anton2785-bit/anton2785-bit-Anton_s-Keyboard/Images/Keyboard case.png

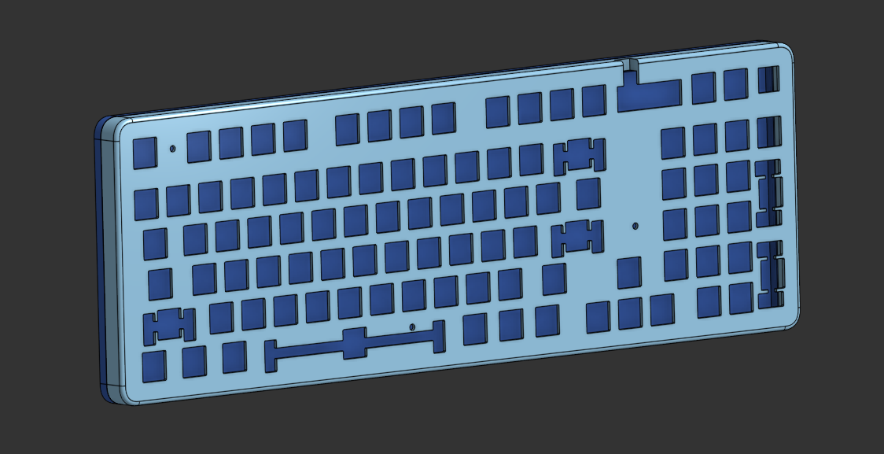
Images/Keyboard case.png
