anton2785-bit/anton2785-bit-Anton_s-Keyboard/Images/Top layer PCB.png

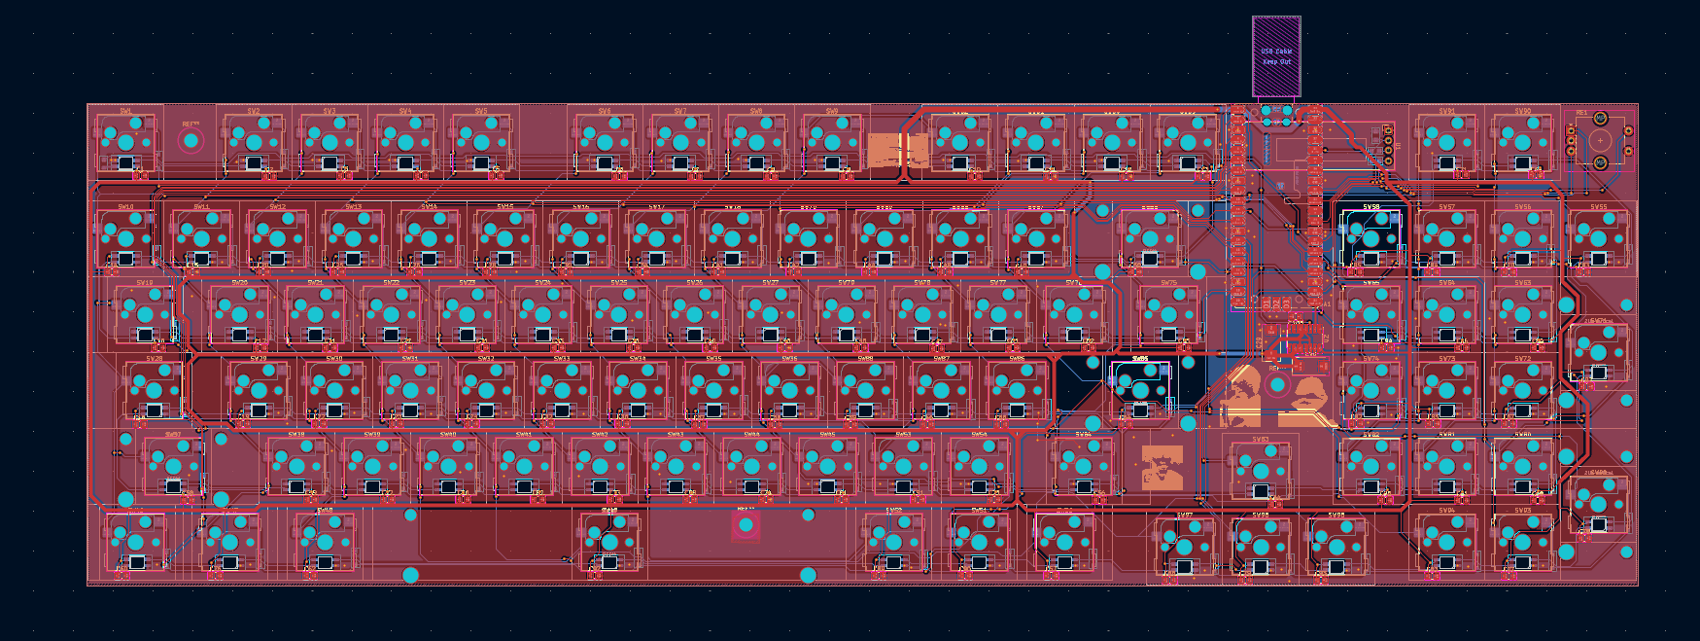
Images/Top layer PCB.png
