anton2785-bit/anton2785-bit-Anton_s-Keyboard/PCB/keyboard.kicad_sch

## KiCad design PCB/keyboard.kicad_sch (2026-03-09)

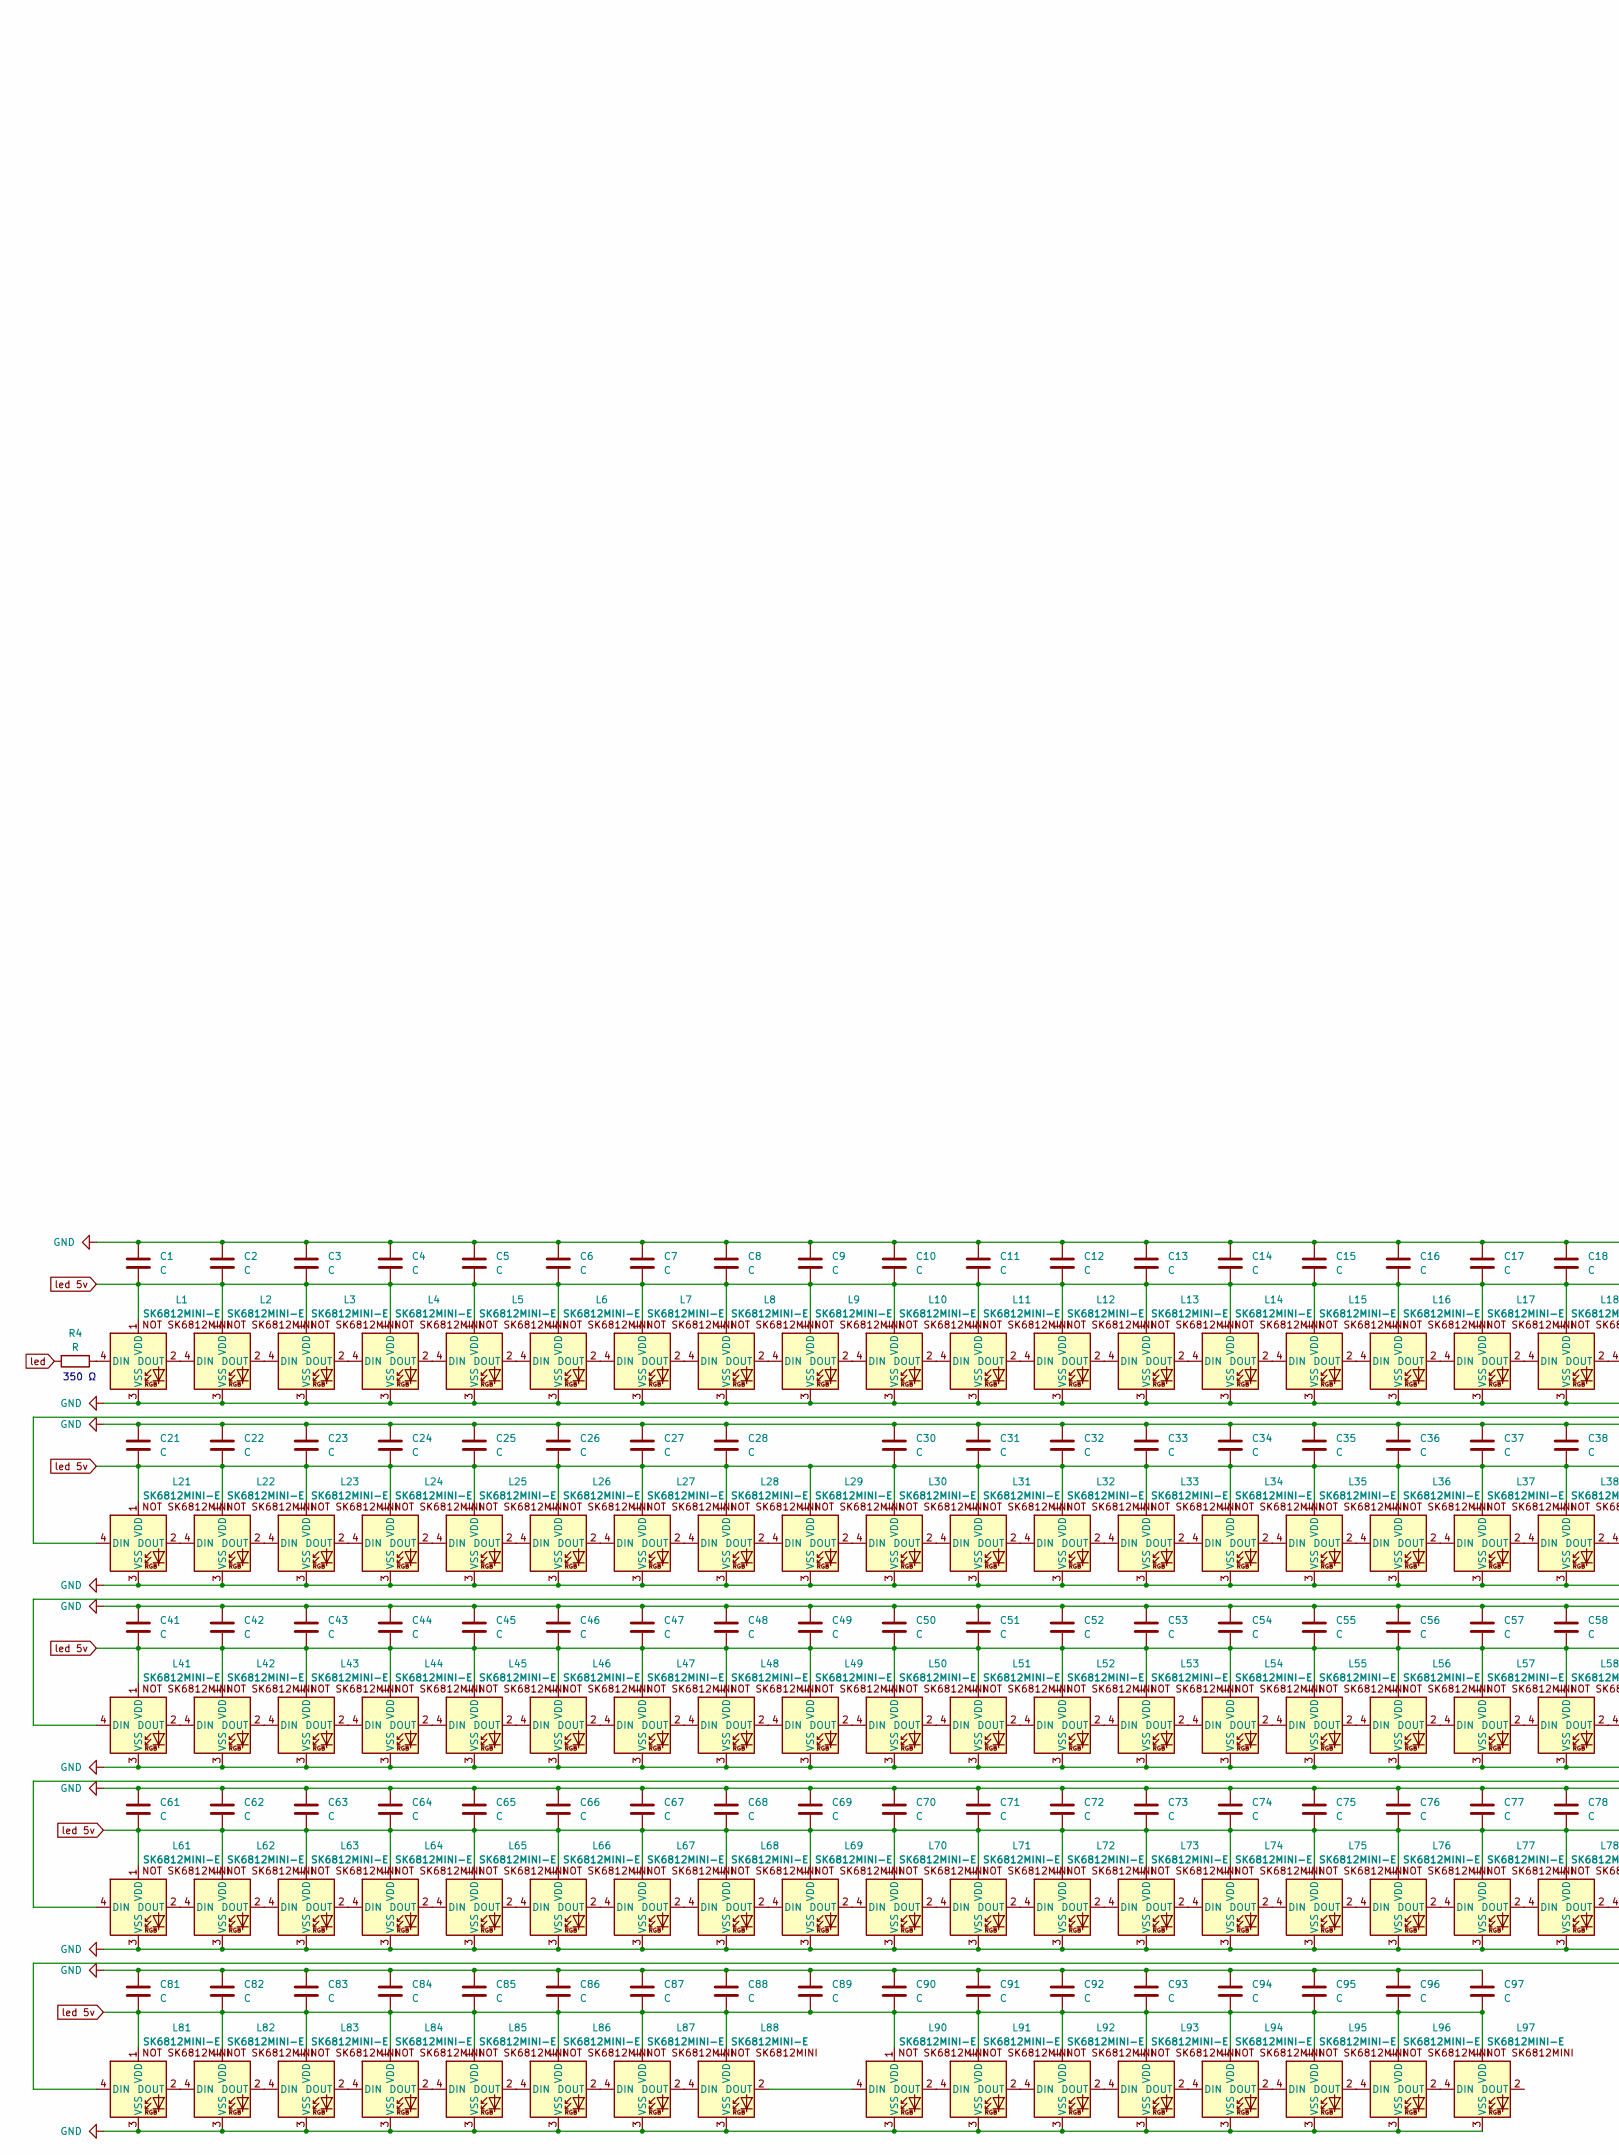
[picture p10: schematic keyboard.kicad_sch, part in row 1, column 1]

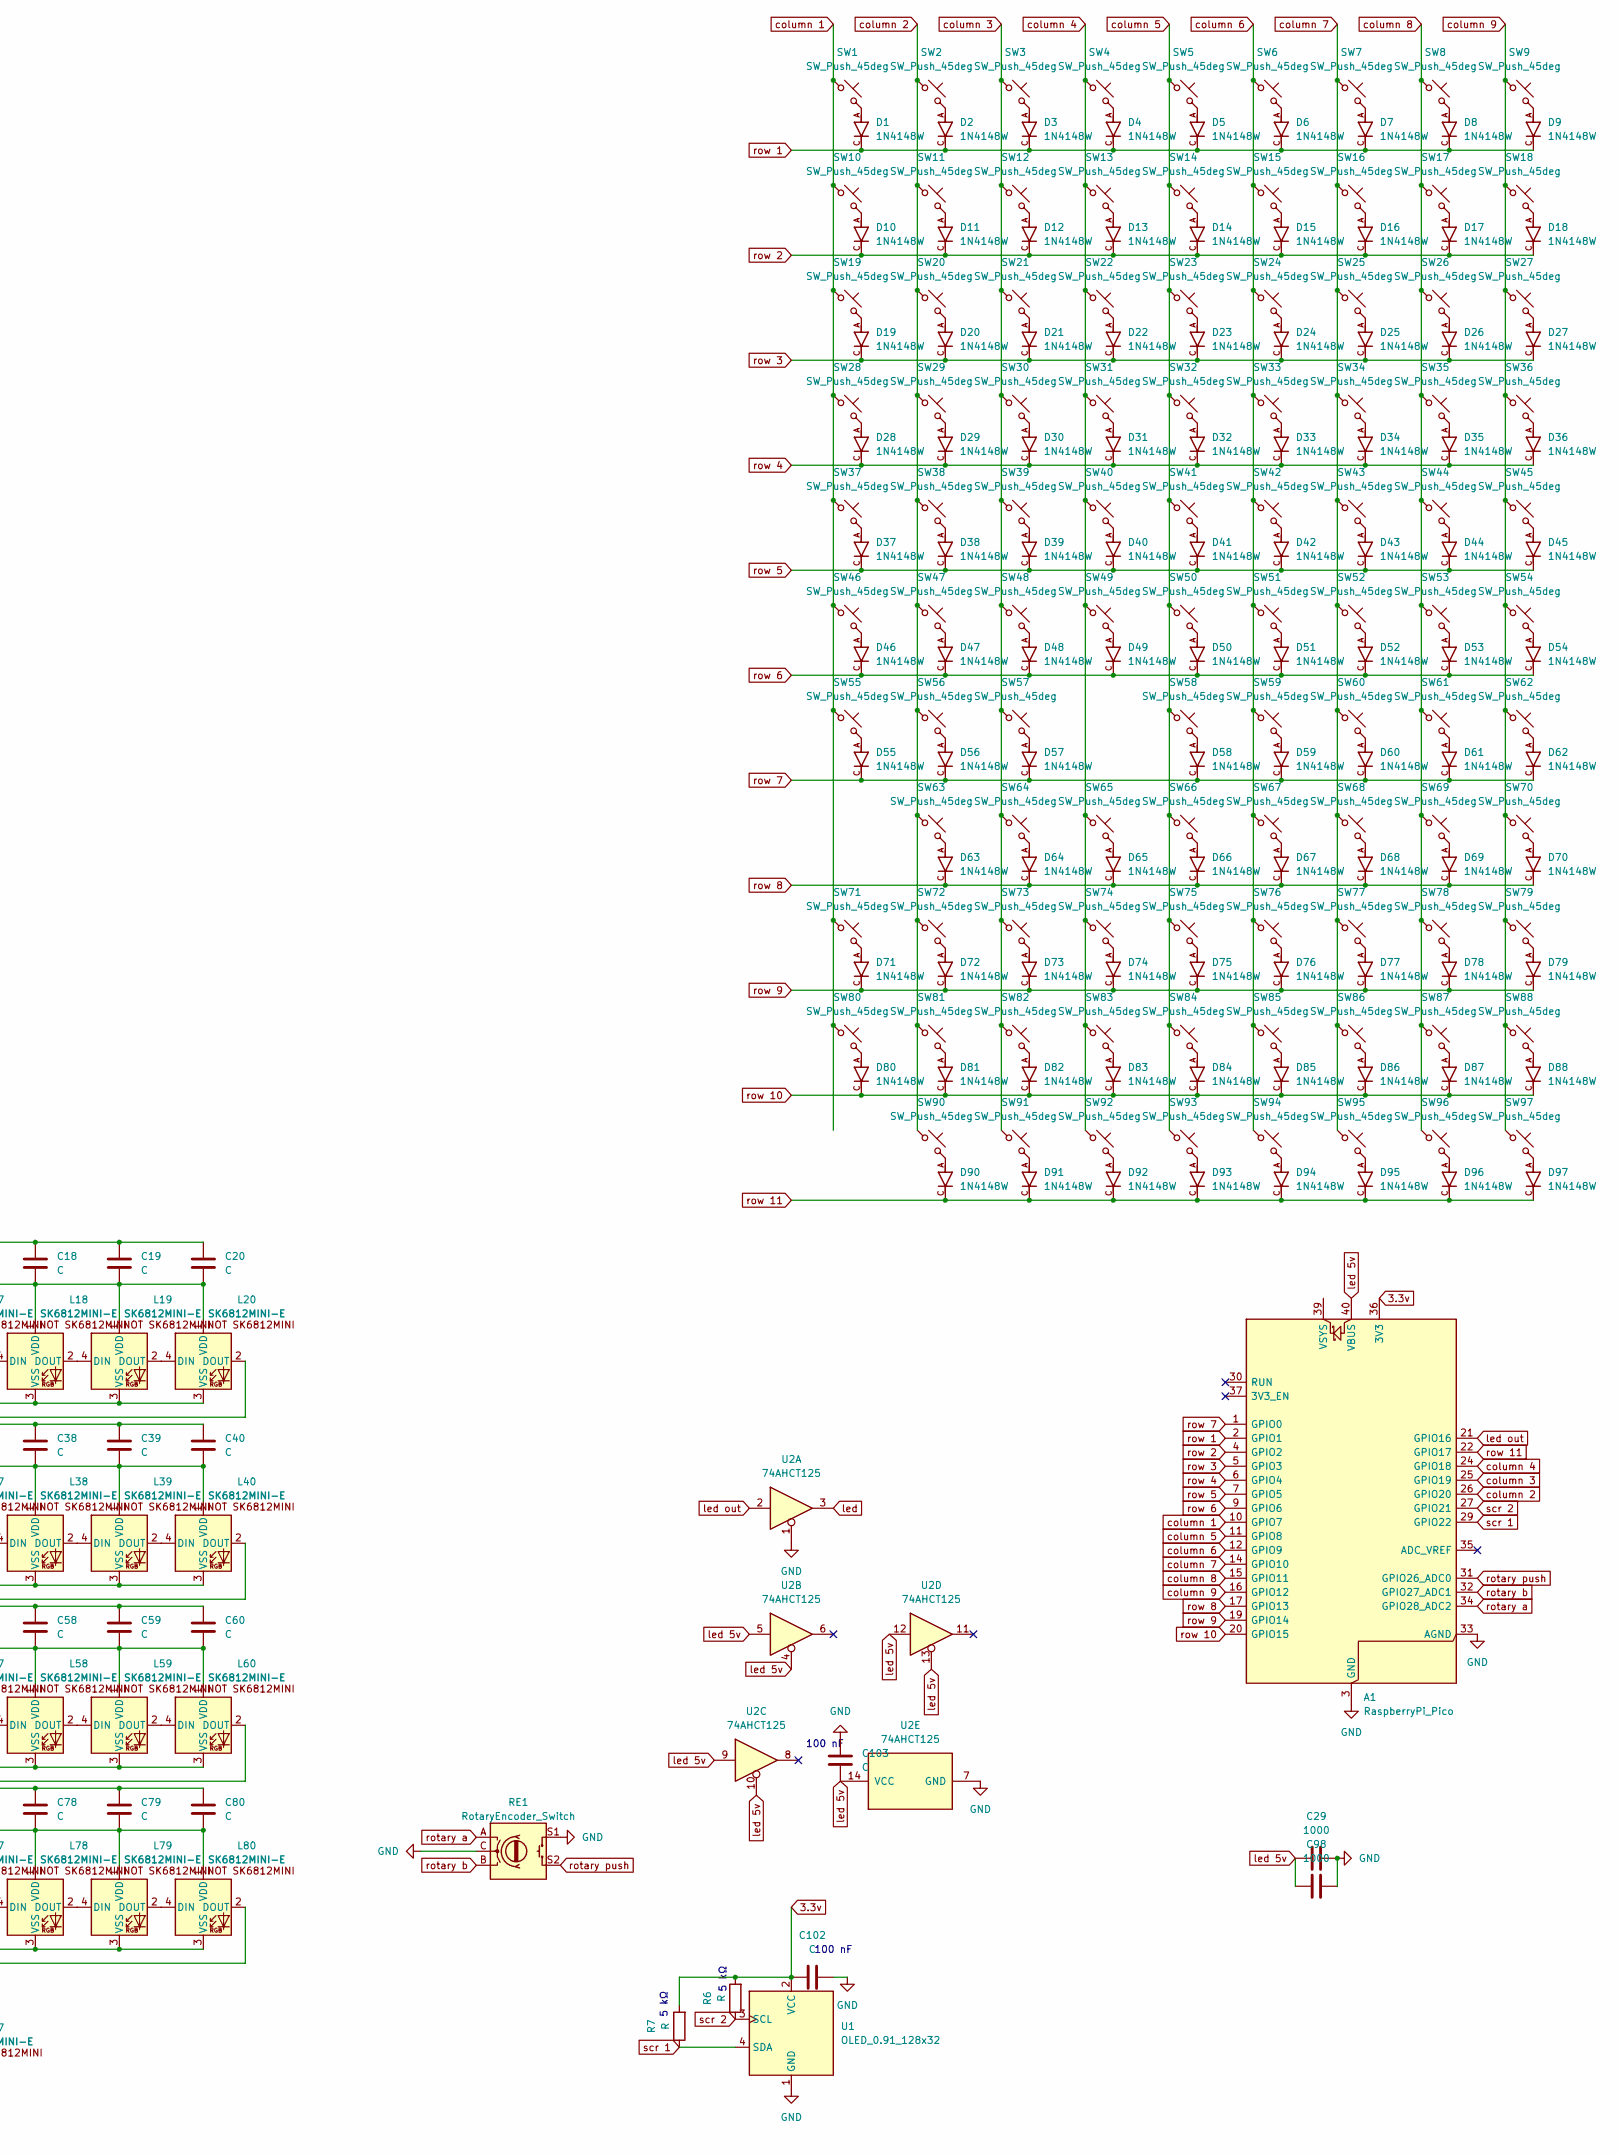
[picture p11: schematic keyboard.kicad_sch, part in row 1, column 2]

Parts:
A1: RaspberryPi_Pico; RaspberryPi_Pico_SMD_HandSolder
C1, C2, C3, C4, C5, C6, C7, C8, C9, C10, C11, C12, C13, C14, C15, C16, C17, C18, C19, C20, C21, C22, C23, C24, C25, C26, C27, C28, C30, C31, C32, C33, C34, C35, C36, C37, C38, C39, C40, C41, C42, C43, C44, C45, C46, C47, C48, C49, C50, C51, C52, C53, C54, C55, C56, C57, C58, C59, C60, C61, C62, C63, C64, C65, C66, C67, C68, C69, C70, C71, C72, C73, C74, C75, C76, C77, C78, C79, C80, C81, C82, C83, C84, C85, C86, C87, C88, C89, C90, C91, C92, C93, C94, C95, C96, C97, C102, C103: C; C_0805_2012Metric_Pad1.18x1.45mm_HandSolder
C29, C98: 1000; CP_EIA-7343-31_Kemet-D_HandSolder
D1, D2, D3, D4, D5, D6, D7, D8, D9, D10, D11, D12, D13, D14, D15, D16, D17, D18, D19, D20, D21, D22, D23, D24, D25, D26, D27, D28, D29, D30, D31, D32, D33, D34, D35, D36, D37, D38, D39, D40, D41, D42, D43, D44, D45, D46, D47, D48, D49, D50, D51, D52, D53, D54, D55, D56, D57, D58, D59, D60, D61, D62, D63, D64, D65, D66, D67, D68, D69, D70, D71, D72, D73, D74, D75, D76, D77, D78, D79, D80, D81, D82, D83, D84, D85, D86, D87, D88, D90, D91, D92, D93, D94, D95, D96, D97: 1N4148W; SODFL3816X120N; PARTREV 2021-07-12
L1, L2, L3, L4, L5, L6, L7, L8, L9, L10, L11, L12, L13, L28, L29, L30, L31, L32, L33, L34, L35, L36, L37, L38, L39, L40, L41, L55, L56, L57, L58, L59, L60, L61, L62, L63, L64, L65, L66, L67, L68, L69, L70, L74, L75, L76, L80, L81: SK6812MINI-E; MX_sk6812_mini_e_v1
L14, L15, L16, L17, L18, L19, L20, L21, L22, L23, L24, L25, L26, L27, L42, L43, L44, L45, L46, L47, L48, L49, L50, L51, L52, L53, L54, L71, L72, L73, L77, L78, L79, L82, L83, L84, L85, L86, L87, L88, L90, L91, L92, L93, L94, L95, L96, L97: SK6812MINI-E; MX_sk6812_mini_e_v1_rotated
R4, R6, R7: R; R_0805_2012Metric_Pad1.20x1.40mm_HandSolder
RE1: RotaryEncoder_Switch; RotaryEncoder_Alps_EC11E-Switch_Vertical_H20mm_CircularMoun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
SW1, SW2, SW3, SW4, SW5, SW6, SW7, SW8, SW9, SW10, SW11, SW12, SW13, SW14, SW15, SW16, SW17, SW18, SW20, SW21, SW22, SW23, SW24, SW25, SW26, SW27, SW29, SW30, SW31, SW32, SW33, SW34, SW35, SW36, SW38, SW39, SW40, SW41, SW42, SW43, SW44, SW45, SW53, SW54, SW55, SW56, SW57, SW58, SW59, SW60, SW61, SW62, SW63, SW64, SW65, SW67, SW68, SW69, SW70, SW72, SW73, SW74, SW76, SW77, SW78, SW79, SW80, SW81, SW82, SW83, SW86, SW87, SW88, SW90, SW91, SW93, SW94, SW95, SW96, SW97: SW_Push_45deg; Hotswap_MX_1.00u
SW19, SW75: SW_Push_45deg; Hotswap_MX_1.50u
SW28, SW84: SW_Push_45deg; Hotswap_MX_1.75u
SW37, SW85: SW_Push_45deg; Hotswap_MX_2.25u
SW46, SW47, SW48, SW50, SW51, SW52: SW_Push_45deg; Hotswap_MX_1.25u
SW49: SW_Push_45deg; Hotswap_MX_6.25u
SW66: SW_Push_45deg; Hotswap_MX_2.00u
SW71, SW92: SW_Push_45deg; Hotswap_MX_2.00u_90deg
U1: OLED_0.91_128x32
U2: 74AHCT125; SOIC-14_3.9x8.7mm_P1.27mm

Connections:
3.3v: A1.36 (3V3), C102.2, R6.2, R7.2, U1.2 (VCC)
GND: A1.3 (GND), A1.8 (GND), A1.13 (GND), A1.18 (GND), A1.23 (GND), A1.28 (GND), A1.33 (AGND), A1.38 (GND), C1.2, C2.2, C3.2, C4.2, C5.2, C6.2, C7.2, C8.2, C9.2, C10.2, C11.2, C12.2, C13.2, C14.2, C15.2, C16.2, C17.2, C18.2, C19.2, C20.2, C21.2, C22.2, C23.2, C24.2, C25.2, C26.2, C27.2, C28.2, C29.2, C30.2, C31.2, C32.2, C33.2, C34.2, C35.2, C36.2, C37.2, C38.2, C39.2, C40.2, C41.2, C42.2, C43.2, C44.2, C45.2, C46.2, C47.2, C48.2, C49.2, C50.2, C51.2, C52.2, C53.2, C54.2, C55.2, C56.2, C57.2, C58.2, C59.2, C60.2, C61.2, C62.2, C63.2, C64.2, C65.2, C66.2, C67.2, C68.2, C69.2, C70.2, C71.2, C72.2, C73.2, C74.2, C75.2, C76.2, C77.2, C78.2, C79.2, C80.2, C81.2, C82.2, C83.2, C84.2, C85.2, C86.2, C87.2, C88.2, C89.2, C90.2, C91.2, C92.2, C93.2, C94.2, C95.2, C96.2, C97.2, C98.2, C102.1, C103.2, L1.3 (VSS), L2.3 (VSS), L3.3 (VSS), L4.3 (VSS), L5.3 (VSS), L6.3 (VSS), L7.3 (VSS), L8.3 (VSS), L9.3 (VSS), L10.3 (VSS), L11.3 (VSS), L12.3 (VSS), L13.3 (VSS), L14.3 (VSS), L15.3 (VSS), L16.3 (VSS), L17.3 (VSS), L18.3 (VSS), L19.3 (VSS), L20.3 (VSS), L21.3 (VSS), L22.3 (VSS), L23.3 (VSS), L24.3 (VSS), L25.3 (VSS), L26.3 (VSS), L27.3 (VSS), L28.3 (VSS), L29.3 (VSS), L30.3 (VSS), L31.3 (VSS), L32.3 (VSS), L33.3 (VSS), L34.3 (VSS), L35.3 (VSS), L36.3 (VSS), L37.3 (VSS), L38.3 (VSS), L39.3 (VSS), L40.3 (VSS), L41.3 (VSS), L42.3 (VSS), L43.3 (VSS), L44.3 (VSS), L45.3 (VSS), L46.3 (VSS), L47.3 (VSS), L48.3 (VSS), L49.3 (VSS), L50.3 (VSS), L51.3 (VSS), L52.3 (VSS), L53.3 (VSS), L54.3 (VSS), L55.3 (VSS), L56.3 (VSS), L57.3 (VSS), L58.3 (VSS), L59.3 (VSS), L60.3 (VSS), L61.3 (VSS), L62.3 (VSS), L63.3 (VSS), L64.3 (VSS), L65.3 (VSS), L66.3 (VSS), L67.3 (VSS), L68.3 (VSS), L69.3 (VSS), L70.3 (VSS), L71.3 (VSS), L72.3 (VSS), L73.3 (VSS), L74.3 (VSS), L75.3 (VSS), L76.3 (VSS), L77.3 (VSS), L78.3 (VSS), L79.3 (VSS), L80.3 (VSS), L81.3 (VSS), L82.3 (VSS), L83.3 (VSS), L84.3 (VSS), L85.3 (VSS), L86.3 (VSS), L87.3 (VSS), L88.3 (VSS), L90.3 (VSS), L91.3 (VSS), L92.3 (VSS), L93.3 (VSS), L94.3 (VSS), L95.3 (VSS), L96.3 (VSS), L97.3 (VSS), RE1.C, RE1.S1, U1.1 (GND), U2.1, U2.7 (GND)
unnamed: D1.A, SW1.2
unnamed: D2.A, SW2.2
unnamed: D3.A, SW3.2
unnamed: D4.A, SW4.2
unnamed: D5.A, SW5.2
unnamed: D6.A, SW6.2
unnamed: D7.A, SW7.2
unnamed: D8.A, SW8.2
unnamed: D9.A, SW9.2
unnamed: D10.A, SW10.2
unnamed: D11.A, SW11.2
unnamed: D12.A, SW12.2
unnamed: D13.A, SW13.2
unnamed: D14.A, SW14.2
unnamed: D15.A, SW15.2
unnamed: D16.A, SW16.2
unnamed: D17.A, SW17.2
unnamed: D18.A, SW18.2
unnamed: D19.A, SW19.2
unnamed: D20.A, SW20.2
unnamed: D21.A, SW21.2
unnamed: D22.A, SW22.2
unnamed: D23.A, SW23.2
unnamed: D24.A, SW24.2
unnamed: D25.A, SW25.2
unnamed: D26.A, SW26.2
unnamed: D27.A, SW27.2
unnamed: D28.A, SW28.2
unnamed: D29.A, SW29.2
unnamed: D30.A, SW30.2
unnamed: D31.A, SW31.2
unnamed: D32.A, SW32.2
unnamed: D33.A, SW33.2
unnamed: D34.A, SW34.2
unnamed: D35.A, SW35.2
unnamed: D36.A, SW36.2
unnamed: D37.A, SW37.2
unnamed: D38.A, SW38.2
unnamed: D39.A, SW39.2
unnamed: D40.A, SW40.2
unnamed: D41.A, SW41.2
unnamed: D42.A, SW42.2
unnamed: D43.A, SW43.2
unnamed: D44.A, SW44.2
unnamed: D45.A, SW45.2
unnamed: D46.A, SW46.2
unnamed: D47.A, SW47.2
unnamed: D48.A, SW48.2
unnamed: D49.A, SW49.2
unnamed: D50.A, SW50.2
unnamed: D51.A, SW51.2
unnamed: D52.A, SW52.2
unnamed: D53.A, SW53.2
unnamed: D54.A, SW54.2
unnamed: D55.A, SW55.2
unnamed: D56.A, SW56.2
unnamed: D57.A, SW57.2
unnamed: D58.A, SW58.2
unnamed: D59.A, SW59.2
unnamed: D60.A, SW60.2
unnamed: D61.A, SW61.2
unnamed: D62.A, SW62.2
unnamed: D63.A, SW63.2
unnamed: D64.A, SW64.2
unnamed: D65.A, SW65.2
unnamed: D66.A, SW66.2
unnamed: D67.A, SW67.2
unnamed: D68.A, SW68.2
unnamed: D69.A, SW69.2
unnamed: D70.A, SW70.2
unnamed: D71.A, SW71.2
unnamed: D72.A, SW72.2
unnamed: D73.A, SW73.2
unnamed: D74.A, SW74.2
unnamed: D75.A, SW75.2
unnamed: D76.A, SW76.2
unnamed: D77.A, SW77.2
unnamed: D78.A, SW78.2
unnamed: D79.A, SW79.2
unnamed: D80.A, SW80.2
unnamed: D81.A, SW81.2
unnamed: D82.A, SW82.2
unnamed: D83.A, SW83.2
unnamed: D84.A, SW84.2
unnamed: D85.A, SW85.2
unnamed: D86.A, SW86.2
unnamed: D87.A, SW87.2
unnamed: D88.A, SW88.2
unnamed: D90.A, SW90.2
unnamed: D91.A, SW91.2
unnamed: D92.A, SW92.2
unnamed: D93.A, SW93.2
unnamed: D94.A, SW94.2
unnamed: D95.A, SW95.2
unnamed: D96.A, SW96.2
unnamed: D97.A, SW97.2
unnamed: L1.2 (DOUT), L2.4 (DIN)
unnamed: L1.4 (DIN), R4.1
unnamed: L2.2 (DOUT), L3.4 (DIN)
unnamed: L3.2 (DOUT), L4.4 (DIN)
unnamed: L4.2 (DOUT), L5.4 (DIN)
unnamed: L5.2 (DOUT), L6.4 (DIN)
unnamed: L6.2 (DOUT), L7.4 (DIN)
unnamed: L7.2 (DOUT), L8.4 (DIN)
unnamed: L8.2 (DOUT), L9.4 (DIN)
unnamed: L10.2 (DOUT), L11.4 (DIN)
unnamed: L9.2 (DOUT), L10.4 (DIN)
unnamed: L11.2 (DOUT), L12.4 (DIN)
unnamed: L12.2 (DOUT), L13.4 (DIN)
unnamed: L13.2 (DOUT), L14.4 (DIN)
unnamed: L14.2 (DOUT), L15.4 (DIN)
unnamed: L15.2 (DOUT), L16.4 (DIN)
unnamed: L16.2 (DOUT), L17.4 (DIN)
unnamed: L17.2 (DOUT), L18.4 (DIN)
unnamed: L18.2 (DOUT), L19.4 (DIN)
unnamed: L19.2 (DOUT), L20.4 (DIN)
unnamed: L20.2 (DOUT), L21.4 (DIN)
unnamed: L21.2 (DOUT), L22.4 (DIN)
unnamed: L22.2 (DOUT), L23.4 (DIN)
unnamed: L23.2 (DOUT), L24.4 (DIN)
unnamed: L24.2 (DOUT), L25.4 (DIN)
unnamed: L25.2 (DOUT), L26.4 (DIN)
unnamed: L26.2 (DOUT), L27.4 (DIN)
unnamed: L27.2 (DOUT), L28.4 (DIN)
unnamed: L28.2 (DOUT), L29.4 (DIN)
unnamed: L29.2 (DOUT), L30.4 (DIN)
unnamed: L30.2 (DOUT), L31.4 (DIN)
unnamed: L31.2 (DOUT), L32.4 (DIN)
unnamed: L32.2 (DOUT), L33.4 (DIN)
unnamed: L33.2 (DOUT), L34.4 (DIN)
unnamed: L34.2 (DOUT), L35.4 (DIN)
unnamed: L35.2 (DOUT), L36.4 (DIN)
unnamed: L36.2 (DOUT), L37.4 (DIN)
unnamed: L37.2 (DOUT), L38.4 (DIN)
unnamed: L38.2 (DOUT), L39.4 (DIN)
unnamed: L39.2 (DOUT), L40.4 (DIN)
unnamed: L40.2 (DOUT), L41.4 (DIN)
unnamed: L41.2 (DOUT), L42.4 (DIN)
unnamed: L42.2 (DOUT), L43.4 (DIN)
unnamed: L43.2 (DOUT), L44.4 (DIN)
unnamed: L44.2 (DOUT), L45.4 (DIN)
unnamed: L45.2 (DOUT), L46.4 (DIN)
unnamed: L46.2 (DOUT), L47.4 (DIN)
unnamed: L47.2 (DOUT), L48.4 (DIN)
unnamed: L48.2 (DOUT), L49.4 (DIN)
unnamed: L49.2 (DOUT), L50.4 (DIN)
unnamed: L50.2 (DOUT), L51.4 (DIN)
unnamed: L51.2 (DOUT), L52.4 (DIN)
unnamed: L52.2 (DOUT), L53.4 (DIN)
unnamed: L53.2 (DOUT), L54.4 (DIN)
unnamed: L54.2 (DOUT), L55.4 (DIN)
unnamed: L55.2 (DOUT), L56.4 (DIN)
unnamed: L56.2 (DOUT), L57.4 (DIN)
unnamed: L57.2 (DOUT), L58.4 (DIN)
unnamed: L58.2 (DOUT), L59.4 (DIN)
unnamed: L59.2 (DOUT), L60.4 (DIN)
unnamed: L60.2 (DOUT), L61.4 (DIN)
unnamed: L61.2 (DOUT), L62.4 (DIN)
unnamed: L62.2 (DOUT), L63.4 (DIN)
unnamed: L63.2 (DOUT), L64.4 (DIN)
unnamed: L64.2 (DOUT), L65.4 (DIN)
unnamed: L65.2 (DOUT), L66.4 (DIN)
unnamed: L66.2 (DOUT), L67.4 (DIN)
unnamed: L67.2 (DOUT), L68.4 (DIN)
unnamed: L68.2 (DOUT), L69.4 (DIN)
unnamed: L69.2 (DOUT), L70.4 (DIN)
unnamed: L70.2 (DOUT), L71.4 (DIN)
unnamed: L71.2 (DOUT), L72.4 (DIN)
unnamed: L72.2 (DOUT), L73.4 (DIN)
unnamed: L73.2 (DOUT), L74.4 (DIN)
unnamed: L74.2 (DOUT), L75.4 (DIN)
unnamed: L75.2 (DOUT), L76.4 (DIN)
unnamed: L76.2 (DOUT), L77.4 (DIN)
unnamed: L77.2 (DOUT), L78.4 (DIN)
unnamed: L78.2 (DOUT), L79.4 (DIN)
unnamed: L79.2 (DOUT), L80.4 (DIN)
unnamed: L80.2 (DOUT), L81.4 (DIN)
unnamed: L81.2 (DOUT), L82.4 (DIN)
unnamed: L82.2 (DOUT), L83.4 (DIN)
unnamed: L83.2 (DOUT), L84.4 (DIN)
unnamed: L84.2 (DOUT), L85.4 (DIN)
unnamed: L85.2 (DOUT), L86.4 (DIN)
unnamed: L86.2 (DOUT), L87.4 (DIN)
unnamed: L87.2 (DOUT), L88.4 (DIN)
unnamed: L88.2 (DOUT), L90.4 (DIN)
unnamed: L90.2 (DOUT), L91.4 (DIN)
unnamed: L91.2 (DOUT), L92.4 (DIN)
unnamed: L92.2 (DOUT), L93.4 (DIN)
unnamed: L93.2 (DOUT), L94.4 (DIN)
unnamed: L94.2 (DOUT), L95.4 (DIN)
unnamed: L95.2 (DOUT), L96.4 (DIN)
unnamed: L96.2 (DOUT), L97.4 (DIN)
column 1: A1.10 (GPIO7), SW1.1, SW10.1, SW19.1, SW28.1, SW37.1, SW46.1, SW55.1, SW71.1, SW80.1
column 2: A1.26 (GPIO20), SW2.1, SW11.1, SW20.1, SW29.1, SW38.1, SW47.1, SW56.1, SW63.1, SW72.1, SW81.1, SW90.1
column 3: A1.25 (GPIO19), SW3.1, SW12.1, SW21.1, SW30.1, SW39.1, SW48.1, SW57.1, SW64.1, SW73.1, SW82.1, SW91.1
column 4: A1.24 (GPIO18), SW4.1, SW13.1, SW22.1, SW31.1, SW40.1, SW49.1, SW65.1, SW74.1, SW83.1, SW92.1
column 5: A1.11 (GPIO8), SW5.1, SW14.1, SW23.1, SW32.1, SW41.1, SW50.1, SW58.1, SW66.1, SW75.1, SW84.1, SW93.1
column 6: A1.12 (GPIO9), SW6.1, SW15.1, SW24.1, SW33.1, SW42.1, SW51.1, SW59.1, SW67.1, SW76.1, SW85.1, SW94.1
column 7: A1.14 (GPIO10), SW7.1, SW16.1, SW25.1, SW34.1, SW43.1, SW52.1, SW60.1, SW68.1, SW77.1, SW86.1, SW95.1
column 8: A1.15 (GPIO11), SW8.1, SW17.1, SW26.1, SW35.1, SW44.1, SW53.1, SW61.1, SW69.1, SW78.1, SW87.1, SW96.1
column 9: A1.16 (GPIO12), SW9.1, SW18.1, SW27.1, SW36.1, SW45.1, SW54.1, SW62.1, SW70.1, SW79.1, SW88.1, SW97.1
led: R4.2, U2.3
led 5v: A1.40 (VBUS), C1.1, C2.1, C3.1, C4.1, C5.1, C6.1, C7.1, C8.1, C9.1, C10.1, C11.1, C12.1, C13.1, C14.1, C15.1, C16.1, C17.1, C18.1, C19.1, C20.1, C21.1, C22.1, C23.1, C24.1, C25.1, C26.1, C27.1, C28.1, C29.1, C30.1, C31.1, C32.1, C33.1, C34.1, C35.1, C36.1, C37.1, C38.1, C39.1, C40.1, C41.1, C42.1, C43.1, C44.1, C45.1, C46.1, C47.1, C48.1, C49.1, C50.1, C51.1, C52.1, C53.1, C54.1, C55.1, C56.1, C57.1, C58.1, C59.1, C60.1, C61.1, C62.1, C63.1, C64.1, C65.1, C66.1, C67.1, C68.1, C69.1, C70.1, C71.1, C72.1, C73.1, C74.1, C75.1, C76.1, C77.1, C78.1, C79.1, C80.1, C81.1, C82.1, C83.1, C84.1, C85.1, C86.1, C87.1, C88.1, C89.1, C90.1, C91.1, C92.1, C93.1, C94.1, C95.1, C96.1, C97.1, C98.1, C103.1, L1.1 (VDD), L2.1 (VDD), L3.1 (VDD), L4.1 (VDD), L5.1 (VDD), L6.1 (VDD), L7.1 (VDD), L8.1 (VDD), L9.1 (VDD), L10.1 (VDD), L11.1 (VDD), L12.1 (VDD), L13.1 (VDD), L14.1 (VDD), L15.1 (VDD), L16.1 (VDD), L17.1 (VDD), L18.1 (VDD), L19.1 (VDD), L20.1 (VDD), L21.1 (VDD), L22.1 (VDD), L23.1 (VDD), L24.1 (VDD), L25.1 (VDD), L26.1 (VDD), L27.1 (VDD), L28.1 (VDD), L29.1 (VDD), L30.1 (VDD), L31.1 (VDD), L32.1 (VDD), L33.1 (VDD), L34.1 (VDD), L35.1 (VDD), L36.1 (VDD), L37.1 (VDD), L38.1 (VDD), L39.1 (VDD), L40.1 (VDD), L41.1 (VDD), L42.1 (VDD), L43.1 (VDD), L44.1 (VDD), L45.1 (VDD), L46.1 (VDD), L47.1 (VDD), L48.1 (VDD), L49.1 (VDD), L50.1 (VDD), L51.1 (VDD), L52.1 (VDD), L53.1 (VDD), L54.1 (VDD), L55.1 (VDD), L56.1 (VDD), L57.1 (VDD), L58.1 (VDD), L59.1 (VDD), L60.1 (VDD), L61.1 (VDD), L62.1 (VDD), L63.1 (VDD), L64.1 (VDD), L65.1 (VDD), L66.1 (VDD), L67.1 (VDD), L68.1 (VDD), L69.1 (VDD), L70.1 (VDD), L71.1 (VDD), L72.1 (VDD), L73.1 (VDD), L74.1 (VDD), L75.1 (VDD), L76.1 (VDD), L77.1 (VDD), L78.1 (VDD), L79.1 (VDD), L80.1 (VDD), L81.1 (VDD), L82.1 (VDD), L83.1 (VDD), L84.1 (VDD), L85.1 (VDD), L86.1 (VDD), L87.1 (VDD), L88.1 (VDD), L90.1 (VDD), L91.1 (VDD), L92.1 (VDD), L93.1 (VDD), L94.1 (VDD), L95.1 (VDD), L96.1 (VDD), L97.1 (VDD), U2.4, U2.5, U2.9, U2.10, U2.12, U2.13, U2.14 (VCC)
led out: A1.21 (GPIO16), U2.2
rotary a: A1.34 (GPIO28_ADC2), RE1.A
rotary b: A1.32 (GPIO27_ADC1), RE1.B
rotary push: A1.31 (GPIO26_ADC0), RE1.S2
row 1: A1.2 (GPIO1), D1.C, D2.C, D3.C, D4.C, D5.C, D6.C, D7.C, D8.C, D9.C
row 2: A1.4 (GPIO2), D10.C, D11.C, D12.C, D13.C, D14.C, D15.C, D16.C, D17.C, D18.C
row 3: A1.5 (GPIO3), D19.C, D20.C, D21.C, D22.C, D23.C, D24.C, D25.C, D26.C, D27.C
row 4: A1.6 (GPIO4), D28.C, D29.C, D30.C, D31.C, D32.C, D33.C, D34.C, D35.C, D36.C
row 5: A1.7 (GPIO5), D37.C, D38.C, D39.C, D40.C, D41.C, D42.C, D43.C, D44.C, D45.C
row 6: A1.9 (GPIO6), D46.C, D47.C, D48.C, D49.C, D50.C, D51.C, D52.C, D53.C, D54.C
row 7: A1.1 (GPIO0), D55.C, D56.C, D57.C, D58.C, D59.C, D60.C, D61.C, D62.C
row 8: A1.17 (GPIO13), D63.C, D64.C, D65.C, D66.C, D67.C, D68.C, D69.C, D70.C
row 9: A1.19 (GPIO14), D71.C, D72.C, D73.C, D74.C, D75.C, D76.C, D77.C, D78.C, D79.C
row 10: A1.20 (GPIO15), D80.C, D81.C, D82.C, D83.C, D84.C, D85.C, D86.C, D87.C, D88.C
row 11: A1.22 (GPIO17), D90.C, D91.C, D92.C, D93.C, D94.C, D95.C, D96.C, D97.C
scr 1: A1.29 (GPIO22), R7.1, U1.4 (SDA)
scr 2: A1.27 (GPIO21), R6.1, U1.3 (SCL)

Notes on the sheet:
5 kΩ
100 nF
350 Ω
